UVA-DSI/sensenet/projects/CCI-SDS/images/mcu-prep.jpg

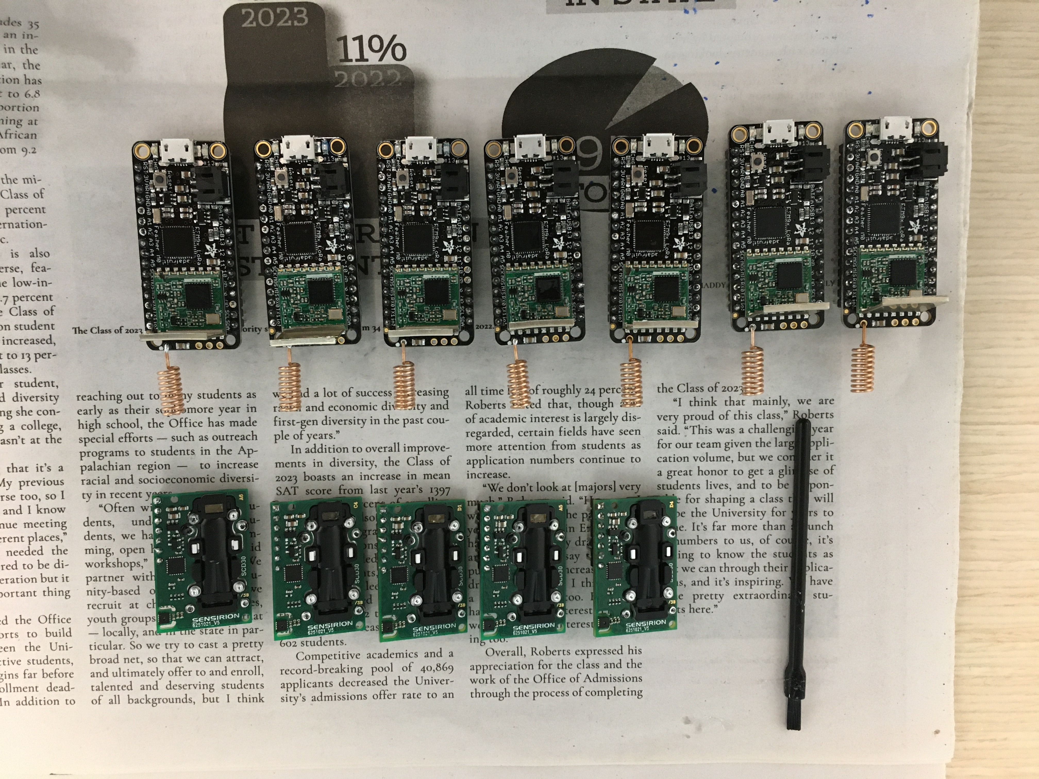
projects/CCI-SDS/images/mcu-prep.jpg
