UVA-DSI/sensenet/projects/CCI-SDS/images/proto_v2.jpg

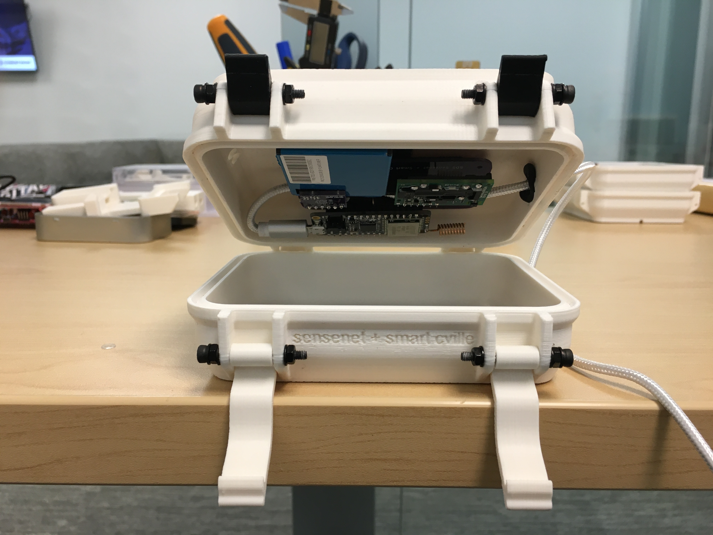
projects/CCI-SDS/images/proto_v2.jpg
