UVA-DSI/sensenet/projects/CCI-SDS/images/scville-hw-kit2.jpg

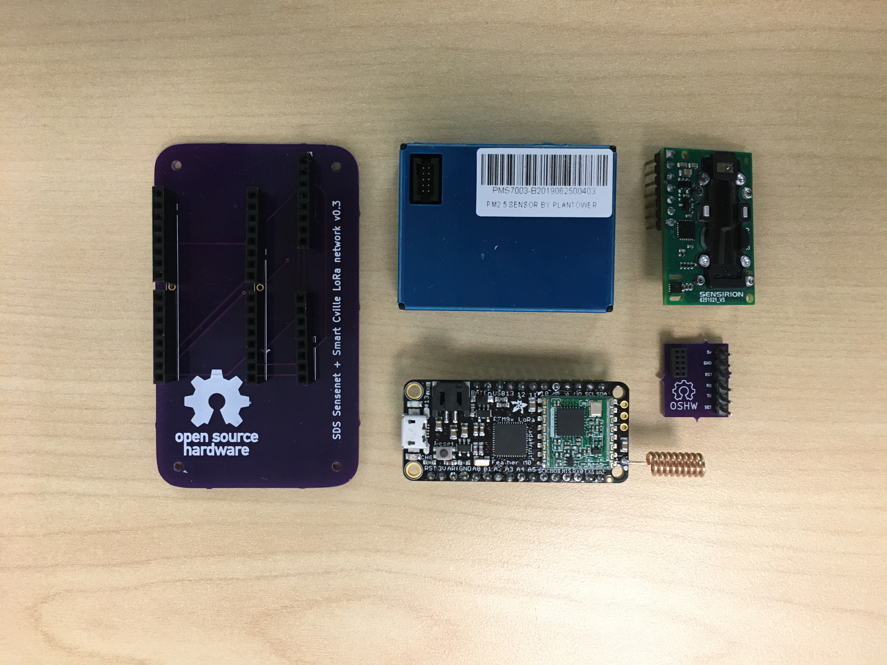
projects/CCI-SDS/images/scville-hw-kit2.jpg
