UVA-DSI/sensenet/projects/CCI-SDS/images/scville-hw-kit-desktop.jpg

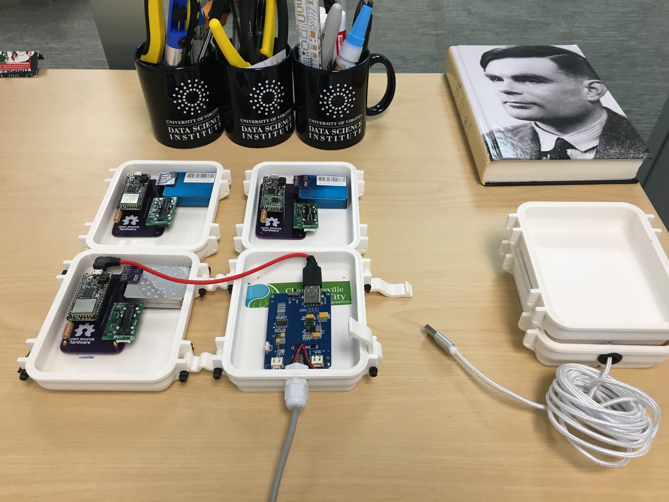
projects/CCI-SDS/images/scville-hw-kit-desktop.jpg
