UVA-DSI/sensenet/projects/CCI-SDS/images/ttn-cville-gateways.png

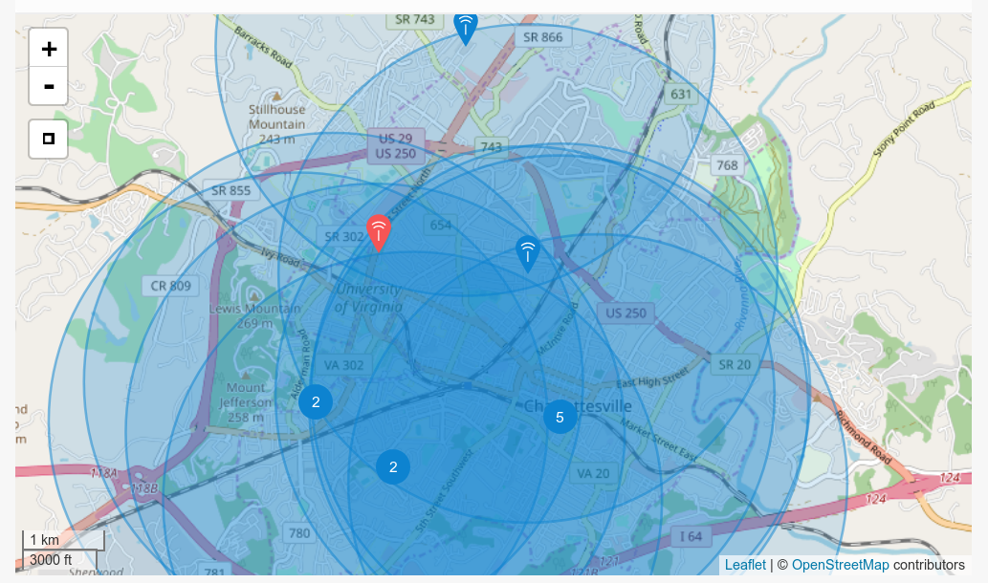
projects/CCI-SDS/images/ttn-cville-gateways.png
