UVA-DSI/sensenet/projects/NPS/board/bigdot.png

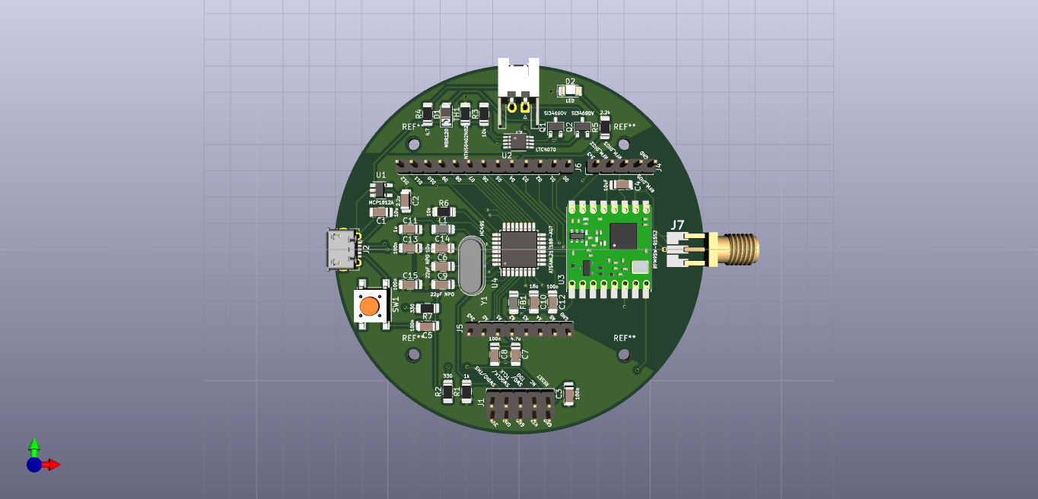
projects/NPS/board/bigdot.png
