UVA-DSI/sensenet/projects/CCI-SDS/images/wiring.png

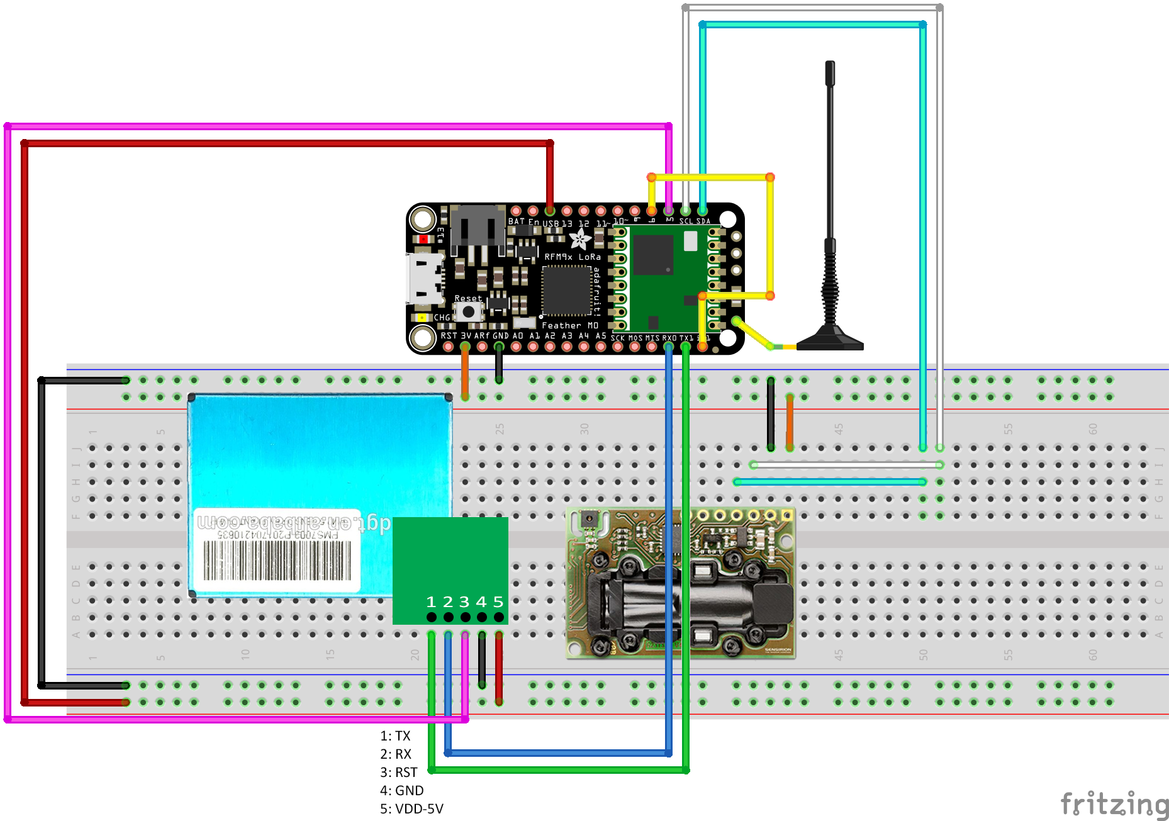
projects/CCI-SDS/images/wiring.png
