UVA-DSI/sensenet/projects/NPS/ostenda-esp32s/ostenda-proto-https-ICS43434/private_settings.h

// WiFi + MQTT credentials
const char* ssid = "wahoo";
const char* passwd = "";
const char* mqtt_server = "";
const char* mqtt_clientID = "esp32s-a1";
const char* mqtt_user = "";
const char* mqtt_passwd = "";
const short mqtt_port = 8883;

static const char ca_fingerprint[]
  PROGMEM = "";

// root CA cert
const char ca_root[] PROGMEM = R"EOF(
-----BEGIN CERTIFICATE-----
-----END CERTIFICATE-----
)EOF";
