UVA-DSI/sensenet/projects/CCI-SDS/sensorboxes/sbox0-abp/ttn-credentials.h

/* 
 *
 * Things Network credentials
 * ABP activation
 *
 */

// application session key
static const u1_t PROGMEM APPSKEY[16] = { };

// network session key
static const u1_t PROGMEM NWKSKEY[16] = { };

// device address
static const u4_t DEVADDR = 0xFFFFFFFF;
