UVA-DSI/sensenet/projects/NPS/SAML21-xplained-board/bootloader/ArduinoCore-samd-1.6.18-beta-b1/bootloaders/zero/board_definitions/board_definitions_XPLAINED_SAML21.h

/*
  Copyright (c) 2017 MattairTech LLC. All right reserved.
  Copyright (c) 2015 Arduino LLC.  All right reserved.
  Copyright (c) 2015 Atmel Corporation/Thibaut VIARD.  All right reserved.

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
  You should have received a copy of the GNU Lesser General Public
  License along with this library; if not, write to the Free Software
  Foundation, Inc., 51 Franklin St, Fifth Floor, Boston, MA  02110-1301  USA
*/

#ifndef _BOARD_DEFINITIONS_H_
#define _BOARD_DEFINITIONS_H_

#include <sam.h>

/* The SAM-BA interface, which is used with both USB CDC and UART (TTL
 * serial), can operate in either binary (default) or terminal mode. If
 * TERMINAL_MODE_ENABLED is defined, additional terminal handling code
 * (add prompt, add \n\r to EOL, number formatting, etc.) will be compiled
 * in. To switch to terminal mode, type 'T#' (you should then see a prompt).
 * Then, type 'V#' to show version information. See README.md for more commands.
 * Size: ~228B. Enabled by default. Disable with 4KB bootloader.
 */
#define TERMINAL_MODE_ENABLED

/* Set SAM_BA_INTERFACE to SAM_BA_USBCDC_ONLY, SAM_BA_UART_ONLY, SAM_BA_NONE, or
 * SAM_BA_BOTH_INTERFACES. With 4KB bootloaders, select only one interface (except
 * when using SDCARD_ENABLED, then set SAM_BA_INTERFACE to SAM_BA_NONE). The C21
 * lacks USB, so set to SAM_BA_UART_ONLY in this case. By default,
 * SAM_BA_USBCDC_ONLY is set (SAM_BA_UART_ONLY with the C21).
 */
#define SAM_BA_INTERFACE              SAM_BA_USBCDC_ONLY

/* If SAM_BA_INTERFACE_USE_PIN is defined, then the associated pin controls which
 * SAM-BA interface is used (if SAM_BA_BOTH_INTERFACES is defined). If only one
 * interface is used, then the pin acts as an enable. In both cases, the value of
 * SAM_BA_INTERFACE_PIN_POLARITY controls the polarity, with values of
 * PIN_POLARITY_ACTIVE_LOW or PIN_POLARITY_ACTIVE_HIGH for a single interface, and
 * PIN_POLARITY_USBCDC_LOW or PIN_POLARITY_USBCDC_HIGH when both interfaces are
 * enabled. PORT can be 0 (Port A) or 1 (Port B). Config can be INPUT, INPUT_PULLUP,
 * or INPUT_PULLDOWN.The USB/UART peripheral and pins will not be setup if the
 * device is not selected/enabled. If no interface is selected by the pin, the LED
 * will blink with status code LED_STATUS_NO_SAM_BA_INTERFACE.
 * Size: ~100B. By default, SAM_BA_INTERFACE_USE_PIN is not defined.
 */
//#define SAM_BA_INTERFACE_USE_PIN
#if (SAM_BA_INTERFACE == SAM_BA_BOTH_INTERFACES)
  // The pin functions as a toggle between the two interfaces
  #define SAM_BA_INTERFACE_PIN_POLARITY      PIN_POLARITY_USBCDC_LOW
#else
  // The pin functions as an enable for the compiled interface
  #define SAM_BA_INTERFACE_PIN_POLARITY      PIN_POLARITY_ACTIVE_LOW
#endif
#define SAM_BA_INTERFACE_PIN_PORT          (0)
#define SAM_BA_INTERFACE_PIN_PIN           (5)
#define SAM_BA_INTERFACE_PIN_CONFIG        INPUT_PULLUP

/* If ARDUINO_EXTENDED_CAPABILITIES is defined and set to 1, 3 additional commands
 * will become available which will speed up programming when using the Arduino
 * IDE or the bossac tool standalone. Set to 0 with 4KB bootloaders.
 * Size: ~904B. This is defined and set to 1 by default (except with 4KB).
 */
#define ARDUINO_EXTENDED_CAPABILITIES   1

/* The clock source must be chosen by setting CLOCKCONFIG_CLOCK_SOURCE to
 * CLOCKCONFIG_32768HZ_CRYSTAL, CLOCKCONFIG_HS_CRYSTAL, CLOCKCONFIG_INTERNAL,
 * or CLOCKCONFIG_INTERNAL_USB. If CLOCKCONFIG_32768HZ_CRYSTAL or
 * CLOCKCONFIG_HS_CRYSTAL is defined, then the PLL will be used. If
 * CLOCKCONFIG_HS_CRYSTAL is defined, then HS_CRYSTAL_FREQUENCY_HERTZ must
 * also be defined with the crystal frequency in Hertz. CLOCKCONFIG_INTERNAL
 * uses the DFLL in open-loop mode, except with the C21 which lacks a DFLL, so
 * the internal 48MHz RC oscillator is used instead. CLOCKCONFIG_INTERNAL_USB
 * can be defined for the D21, D11, L21, or D51. It will also use the DFLL in
 * open-loop mode, except when connected to a USB port with data lines (and
 * not suspended), where it will calibrate against the USB SOF signal.
 */
#define CLOCKCONFIG_CLOCK_SOURCE    CLOCKCONFIG_INTERNAL_USB

/* Master clock frequency (also Fcpu frequency). With the D51,
 * this can be either 120000000ul or 48000000ul. See README.md.
 */
#define VARIANT_MCK                       (48000000ul)

/* The fine calibration value for DFLL open-loop mode is defined here.
 * The coarse calibration value is loaded from NVM OTP (factory calibration values).
 */
#define NVM_SW_CALIB_DFLL48M_FINE_VAL     (512)

/* If USB_VENDOR_STRINGS_ENABLED is defined, then STRING_MANUFACTURER and
 * STRING_PRODUCT will be sent to the host.
 * Size: ~228B. By default, USB_VENDOR_STRINGS_ENABLED is defined (including 4KB).
 */
#define USB_VENDOR_STRINGS_ENABLED
#define STRING_MANUFACTURER "UVA SDS Librelab"
#define STRING_PRODUCT "Big Dot"

/* If USB CDC is used, then the USB vendor ID (VID) and product ID (PID) must be set. */
#define USB_VID_HIGH   0x00
#define USB_VID_LOW    0x00
#define USB_PID_HIGH   0x00
#define USB_PID_LOW    0x00

/* BOOT_USART_SERCOM_INSTANCE must be a single digit representing the SERCOM number.
 * See board_driver_serial.h for BOOT_USART_PAD_SETTINGS values. When setting
 * BOOT_USART_PADx defines, consult the appropriate header file from CMSIS-Atmel (ie:
 * ~/arduino15/packages/MattairTech_Arduino/tools/CMSIS-Atmel/1.0.0-mattairtech-2/
 * CMSIS/Device/ATMEL/sam<d21|d51|c21|l21|d11>/include/<YOUR_CHIP>.h). Use PINMUX_UNUSED
 * if not used. By default, this interface is not enabled (except with the C21).
 */
#define BOOT_USART_SERCOM_INSTANCE        4
#define BOOT_USART_PAD_SETTINGS           UART_RX_PAD1_TX_PAD0
#define BOOT_USART_PAD3                   PINMUX_UNUSED
#define BOOT_USART_PAD2                   PINMUX_UNUSED
#define BOOT_USART_PAD1                   PINMUX_PB09D_SERCOM4_PAD1
#define BOOT_USART_PAD0                   PINMUX_PB08D_SERCOM4_PAD0

#ifndef SDCARD_ENABLED
//#define SDCARD_ENABLED
#endif

/* If SDCARD_ENABLED is defined, then all SDCARD_SPI_* defines must also be set.
 * When setting SDCARD_SPI_PADx defines, consult the appropriate header file
 * from CMSIS-Atmel (ie: ~/arduino15/packages/MattairTech_Arduino/tools/CMSIS-
 * Atmel/1.0.0-mattairtech-2/CMSIS/Device/ATMEL/sam<d21|d51|c21|l21|d11>/include/
 * <YOUR_CHIP>.h). SDCARD_SPI_PAD_SETTINGS values are in SDCard/diskio.h.
 * When using SDCARD_USE_PIN1 or SDCARD_USE_PIN2, the SPI peripheral and
 * associated pins are only initialized if either pin is active.
 */
#define SDCARD_SPI_SERCOM_INSTANCE      5
#if (SAMD51)
  #define SDCARD_SPI_PAD_SETTINGS         SPI_RX_PAD3_TX_PAD0_SCK_PAD1
  #define SDCARD_SPI_PAD0                 PINMUX_PA23D_SERCOM5_PAD0
  #define SDCARD_SPI_PAD1                 PINMUX_PA22D_SERCOM5_PAD1
  #define SDCARD_SPI_PAD2                 PINMUX_UNUSED
  #define SDCARD_SPI_PAD3                 PINMUX_PA21C_SERCOM5_PAD3
#else
  #define SDCARD_SPI_PAD_SETTINGS         SPI_RX_PAD0_TX_PAD2_SCK_PAD3
  #define SDCARD_SPI_PAD0                 PINMUX_PB30D_SERCOM5_PAD0
  #define SDCARD_SPI_PAD1                 PINMUX_UNUSED
  #define SDCARD_SPI_PAD2                 PINMUX_PB22D_SERCOM5_PAD2
  #define SDCARD_SPI_PAD3                 PINMUX_PB23D_SERCOM5_PAD3
#endif

/* If SDCARD_ENABLED is defined, then SDCARD_SPI_CS_PORT and SDCARD_SPI_CS_PIN
 * must also be defined. PORT can be 0 (Port A) or 1 (Port B).
 */
#define SDCARD_SPI_CS_PORT              (1)
#define SDCARD_SPI_CS_PIN               (31)

/*
 * If BOOT_DOUBLE_TAP_ENABLED is defined the bootloader is started by quickly
 * tapping two times on the reset button (within 1/2 second).
 * Size: ~96B. Enabled by default.
 */
#define BOOT_DOUBLE_TAP_ENABLED

/*
 * If BOARD_LED_FADE_ENABLED is defined, then the main LED produces a PWM fade in an
 * "M-wave" pattern, otherwise, it simply turns on (if enabled). When the SD bootloader
 * is running, the fading will be twice as fast as the SAM-BA interface (USB CDC or UART).
 * Size: ~160B. Enabled by default.
 */
#define BOARD_LED_FADE_ENABLED

#endif // _BOARD_DEFINITIONS_H_
