UVA-DSI/sensenet/projects/NPS/SAML21-xplained-board/bootloader/ArduinoCore-samd-1.6.18-beta-b1/variants/XPLAINED_SAML21/variant.h

/*
  Copyright (c) 2014-2015 Arduino LLC.  All right reserved.

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
  You should have received a copy of the GNU Lesser General Public
  License along with this library; if not, write to the Free Software
  Foundation, Inc., 51 Franklin St, Fifth Floor, Boston, MA  02110-1301  USA
*/

#ifndef _VARIANT_XPLAINED_SAML21_
#define _VARIANT_XPLAINED_SAML21_

/* The definitions here need the MattairTech SAMD core >=1.6.8.
 * The format is different than the stock Arduino SAMD core,
 * which uses ARDUINO_SAMD_VARIANT_COMPLIANCE instead.
 */
#define MATTAIRTECH_ARDUINO_SAMD_VARIANT_COMPLIANCE 10608

/*----------------------------------------------------------------------------
 *        Clock Configuration
 *----------------------------------------------------------------------------*/

/* Master clock frequency (also Fcpu frequency). With the D51, this can be
 * either 120000000ul or 48000000ul (selected in the menu). See README.md.
 */
#define VARIANT_MCK                       (F_CPU)

/* The fine calibration value for DFLL open-loop mode is defined here.
 * The coarse calibration value is loaded from NVM OTP (factory calibration values).
 */
#define NVM_SW_CALIB_DFLL48M_FINE_VAL     (512)

/*----------------------------------------------------------------------------
 *        Headers
 *----------------------------------------------------------------------------*/

#include "WVariant.h"
#include "sam.h"

#ifdef __cplusplus
#include "SERCOM.h"
#include "Uart.h"
#endif // __cplusplus

#ifdef __cplusplus
extern "C"
{
#endif // __cplusplus

/*----------------------------------------------------------------------------
 *        Pins
 *----------------------------------------------------------------------------*/

// Number of pins defined in PinDescription array
#define NUM_PIN_DESCRIPTION_ENTRIES     (50u)

#define PINS_COUNT           NUM_PIN_DESCRIPTION_ENTRIES
#define NUM_DIGITAL_PINS     PINS_COUNT
#define NUM_ANALOG_INPUTS    (18u)
#define NUM_ANALOG_OUTPUTS   (2u)

#define analogInputToDigitalPin(p)  (p)

#define digitalPinToPort(P)        ( &(PORT->Group[g_APinDescription[P].ulPort]) )
#define digitalPinToBitMask(P)     ( 1 << g_APinDescription[P].ulPin )
#define portOutputRegister(port)   ( &(port->OUT.reg) )
#define portInputRegister(port)    ( &(port->IN.reg) )
#define portModeRegister(port)     ( &(port->DIR.reg) )
#define digitalPinHasPWM(P)        ( (g_APinDescription[P].ulPinAttribute & PIN_ATTR_TIMER_PWM) == PIN_ATTR_TIMER_PWM )

/* LEDs
 * None of these defines are currently used by the core.
 * XPLAINED onboard LED is on pin 23 / PB10.
 * The RX and TX LEDs are not present.
 * You may optionally add them to any free pins.
 */
#define PIN_LED_13           (10u)
#define PIN_LED              PIN_LED_13
#define PIN_LED2             PIN_LED_RXL
#define PIN_LED3             PIN_LED_TXL
#define LED_BUILTIN          PIN_LED_13

/*
 * Analog pins
 */
#define PIN_A0               (0ul)
#define PIN_A1               (1ul)
#define PIN_A2               (2ul)
#define PIN_A3               (3ul)
#define PIN_A4               (4ul)
#define PIN_A5               (5ul)
#define PIN_A6               (6ul)
#define PIN_A7               (7ul)
#define PIN_A8               (8ul)
#define PIN_A9               (9ul)
#define PIN_A10              (10ul)
#define PIN_A11              (11ul)
#define PIN_A34              (34ul)
#define PIN_A35              (35ul)
#define PIN_A36              (36ul)
#define PIN_A37              (37ul)
#define PIN_A38              (38ul)
#define PIN_A49              (49ul)
#define PIN_DAC0             (2ul)
#define PIN_DAC1             (5ul)

static const uint8_t A0   = PIN_A0;
static const uint8_t A1   = PIN_A1;
static const uint8_t A2   = PIN_A2;
static const uint8_t A3   = PIN_A3;
static const uint8_t A4   = PIN_A4;
static const uint8_t A5   = PIN_A5;
static const uint8_t A6   = PIN_A6;
static const uint8_t A7   = PIN_A7;
static const uint8_t A8   = PIN_A8;
static const uint8_t A9   = PIN_A9;
static const uint8_t A10  = PIN_A10;
static const uint8_t A11  = PIN_A11;
static const uint8_t A34  = PIN_A34;
static const uint8_t A35  = PIN_A35;
static const uint8_t A36  = PIN_A36;
static const uint8_t A37  = PIN_A37;
static const uint8_t A38  = PIN_A38;
static const uint8_t A49  = PIN_A49;
static const uint8_t DAC0 = PIN_DAC0;
static const uint8_t DAC1 = PIN_DAC1;

#define ADC_RESOLUTION		12

// #define REMAP_ANALOG_PIN_ID(pin)	if ( pin < A0 ) pin += A0

/* Set default analog voltage reference */
#define VARIANT_AR_DEFAULT	AR_DEFAULT

/* Reference voltage pins (define even if not enabled with PIN_ATTR_REF in the PinDescription table) */
#define REFA_PIN    (3ul)
#define REFB_PIN    (4ul)

// The ATN pin may be used in the future as the first SPI chip select.
// On boards that do not have the Arduino physical form factor, it can to set to any free pin.
#define PIN_ATN              (21ul)
static const uint8_t ATN = PIN_ATN;

/*
 * Serial interfaces
 */

// Serial1
#define PIN_SERIAL1_RX       (31ul)
#define PIN_SERIAL1_TX       (18ul)
#define PAD_SERIAL1_TX       (UART_TX_PAD_2)
#define PAD_SERIAL1_RX       (SERCOM_RX_PAD_3)
#define SERCOM_INSTANCE_SERIAL1       &sercom1

// Serial2
#define PIN_SERIAL2_RX       (36ul)
#define PIN_SERIAL2_TX       (35ul)
#define PAD_SERIAL2_TX       (UART_TX_PAD_2)
#define PAD_SERIAL2_RX       (SERCOM_RX_PAD_3)
#define SERCOM_INSTANCE_SERIAL2       &sercom0

// Serial3 (a third serial is not available with the D51 on this board)
#define PIN_SERIAL3_RX       (9ul)
#define PIN_SERIAL3_TX       (8ul)
#define PAD_SERIAL3_TX       (UART_TX_PAD_0)
#define PAD_SERIAL3_RX       (SERCOM_RX_PAD_1)

#define SERCOM_INSTANCE_SERIAL3       &sercom4

/*
 * SPI Interfaces
 */
#if defined(TWO_SPI)
#define SPI_INTERFACES_COUNT 2
#elif defined(THREE_SPI)
#define SPI_INTERFACES_COUNT 3
#else
#define SPI_INTERFACES_COUNT 1
#endif

#define PIN_SPI_MISO         (43u)
#define PIN_SPI_MOSI         (45u)
#define PIN_SPI_SCK          (44u)
#define PIN_SPI_SS           (46u)
#define PAD_SPI_TX           SPI_PAD_2_SCK_3
#define PAD_SPI_RX           SERCOM_RX_PAD_0
#define PERIPH_SPI           sercom5

static const uint8_t SS   = PIN_SPI_SS ;        // The SERCOM SS PAD is available on this pin but HW SS isn't used. Set here only for reference.
static const uint8_t MOSI = PIN_SPI_MOSI ;
static const uint8_t MISO = PIN_SPI_MISO ;
static const uint8_t SCK  = PIN_SPI_SCK ;

#define PIN_SPI1_MISO         (12u)
#define PIN_SPI1_MOSI         (10u)
#define PIN_SPI1_SCK          (11u)
#define PIN_SPI1_SS           (13u)
#define PAD_SPI1_TX           SPI_PAD_2_SCK_3
#define PAD_SPI1_RX           SERCOM_RX_PAD_0
#define PERIPH_SPI1           sercom2

static const uint8_t SS1   = PIN_SPI1_SS ;	// The SERCOM SS PAD is available on this pin but HW SS isn't used. Set here only for reference.
static const uint8_t MOSI1 = PIN_SPI1_MOSI ;
static const uint8_t MISO1 = PIN_SPI1_MISO ;
static const uint8_t SCK1  = PIN_SPI1_SCK ;

/*
 * Wire Interfaces
 */
#if defined(TWO_WIRE)
#define WIRE_INTERFACES_COUNT 2
#elif defined(THREE_WIRE)
#define WIRE_INTERFACES_COUNT 3
#else
#define WIRE_INTERFACES_COUNT 1
#endif

#define PIN_WIRE_SDA         (16u)
#define PIN_WIRE_SCL         (17u)
#define PERIPH_WIRE          sercom3
#define WIRE_IT_HANDLER      SERCOM3_Handler

static const uint8_t SDA = PIN_WIRE_SDA;
static const uint8_t SCL = PIN_WIRE_SCL;

#define PIN_WIRE1_SDA         (12u)
#define PIN_WIRE1_SCL         (13u)
#define PERIPH_WIRE1          sercom2
#define WIRE1_IT_HANDLER      SERCOM2_Handler

static const uint8_t SDA1 = PIN_WIRE1_SDA;
static const uint8_t SCL1 = PIN_WIRE1_SCL;

/*
 * USB - Define PIN_USB_HOST_ENABLE to assert the defined pin to
 * PIN_USB_HOST_ENABLE_VALUE during startup. Leave undefined to disable this pin.
 */
#define PIN_USB_DM                      (24ul)
#define PIN_USB_DP                      (25ul)
//#define PIN_USB_HOST_ENABLE             (14ul)
#define PIN_USB_HOST_ENABLE_VALUE	0

/*
 * I2S Interfaces
 * SAMD51, PDM, and MCLK support will be added hopefully March 2018
 */

#define I2S_INTERFACES_COUNT  1
#define I2S_DEVICE            0
//#define I2S1_DEVICE           1
#define I2S_CLOCK_GENERATOR   7
//#define I2S1_CLOCK_GENERATOR  8
//#define PIN_I2S_MCK         (32u)
#define PIN_I2S_SCK         (20u)
#define PIN_I2S_FS          (21u)
#define PIN_I2S_SD          (19u)
//#define PIN_I2S1_MCK         (39u)
//#define PIN_I2S1_SCK         (40u)
//#define PIN_I2S1_FS          (41u)
//#define PIN_I2S1_SD          (33u)

#ifdef __cplusplus
}
#endif


/*----------------------------------------------------------------------------
 *        Arduino objects - C++ only
 *----------------------------------------------------------------------------*/

#ifdef __cplusplus

/*	=========================
 *	===== SERCOM DEFINITION
 *	=========================
*/
extern SERCOM sercom0;
extern SERCOM sercom1;
extern SERCOM sercom2;
extern SERCOM sercom3;
extern SERCOM sercom4;
extern SERCOM sercom5;

extern Uart Serial1;
extern Uart Serial2;
extern Uart Serial3;

#endif

// These serial port names are intended to allow libraries and architecture-neutral
// sketches to automatically default to the correct port name for a particular type
// of use.  For example, a GPS module would normally connect to SERIAL_PORT_HARDWARE_OPEN,
// the first hardware serial port whose RX/TX pins are not dedicated to another use.
//
// SERIAL_PORT_MONITOR        Port which normally prints to the Arduino Serial Monitor
//
// SERIAL_PORT_USBVIRTUAL     Port which is USB virtual serial
//
// SERIAL_PORT_LINUXBRIDGE    Port which connects to a Linux system via Bridge library
//
// SERIAL_PORT_HARDWARE       Hardware serial port, physical RX & TX pins.
//
// SERIAL_PORT_HARDWARE_OPEN  Hardware serial ports which are open for use.  Their RX & TX
//                            pins are NOT connected to anything by default.
#define SERIAL_PORT_USBVIRTUAL      SerialUSB

// SERIAL_PORT_MONITOR seems to be used only by the USB Host library (as of 1.6.5).
// It normally allows debugging output on the USB programming port, while the USB host uses the USB native port.
// The programming port is connected to a hardware UART through a USB-Serial bridge (EDBG chip) on the Zero.
// Boards that do not have the EDBG chip will have to connect a USB-TTL serial adapter to 'Serial' to get
// the USB Host debugging output.
#define SERIAL_PORT_MONITOR         Serial1

// Serial has no physical pins broken out, so it's not listed as HARDWARE port
#define SERIAL_PORT_HARDWARE        Serial1
#define SERIAL_PORT_HARDWARE_OPEN   Serial1

// The Xeno does not have the EDBG support chip, which provides a USB-UART bridge
// accessible using Serial (the Arduino serial monitor is normally connected to this).
// So, the USB virtual serial port (SerialUSB) must be used to communicate with the host.
// Because most sketches use Serial to print to the monitor, it is aliased to SerialUSB.
// Remember to use while(!Serial); to wait for a connection before Serial printing.
// When USB CDC is enabled, Serial refers to SerialUSB, otherwise it refers to Serial1.

#if defined(CDC_ONLY) || defined(CDC_HID) || defined(WITH_CDC)
    #define Serial                      SerialUSB
#else
    #define Serial                      Serial1
#endif
#endif

#endif /* _VARIANT_XPLAINED_SAML21_ */
