UVA-DSI/sensenet/sensorboxes/sbox-gps-test/ttn-credentials.h

/* 
 *
 * TTN credentials
 * 
 */

#define FILLME 0

// application id 
static const u1_t PROGMEM APPEUI[8]= { FILLME };

// dev id 
static const u1_t PROGMEM DEVEUI[8]= { FILLME };

// application key
static const u1_t PROGMEM APPKEY[16] = { FILLME };
